curiouselectric/SolarSensor/Solar Sensor Firmware/ATMega328_Solar_Sensor_Ave_CRC_v4/solar_data.h

#pragma once

#include <stdio.h>
#include <Arduino.h>
#include "config.h"

class data_channel {
  public:
    int   id;
    float data_1s;
    float data_10s;
    float data_60s;
    float data_600s;
    float data_3600s;
    float data_min;     // Holds the minimum value ever recorded until reset
                          // Once read and recorded then this value is reset 
    float data_max;     // Holds the maximum value ever recorded until reset
                          // Once read and recorded then this value is reset 
    float data_1s_holder;
    float data_10s_holder;
    float data_60s_holder;
    float data_600s_holder;
    float data_3600s_holder;

    float   sensor_temperature;
    
    // Irradiance conversion values
    float solar_conv_m;  // The conversion is y=mx+c, with the m and c here.
    float solar_conv_c;
    
    int send_solar_data = 5;   // This int sets if the wind speed data will be sent each time. If = 5 then no data sent,
                                    // if = 0 then 1s, = 1 then 10s = 2 then 60s if =3 then 600s if = 4 then 3600s
                                    // This is updated in EEPROM when set

    // Temperature conversion values
    float solar_tempcon_percentage; 
    float solar_tempcon_rated_c;
    bool  solar_tempcon_flag;
                                    
    
    // This is the constructor
    data_channel() {
      data_1s = 0; data_10s = 0; data_60s = 0; data_600s = 0; data_3600s = 0; 
      data_min = 99999; data_max = -99999;
    }
};
